threedaymonk/pipistrelle/software/wavetable/src/table.cpp

#include <stdint.h>
extern const int16_t wavetable[8][8][256] = {
  {
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
};
